Alberto0235/USB3.2-Hub-4Port/Images/Stackup.png

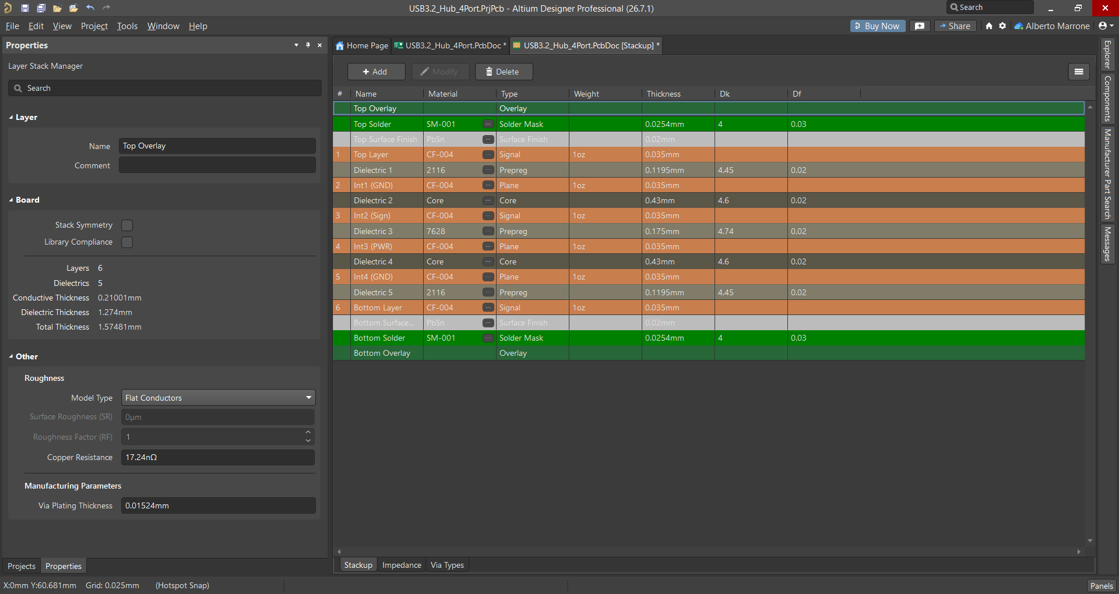
Images/Stackup.png
