Alberto0235/USB3.2-Hub-4Port/Images/Bringup_PowerMeter_Setup.png

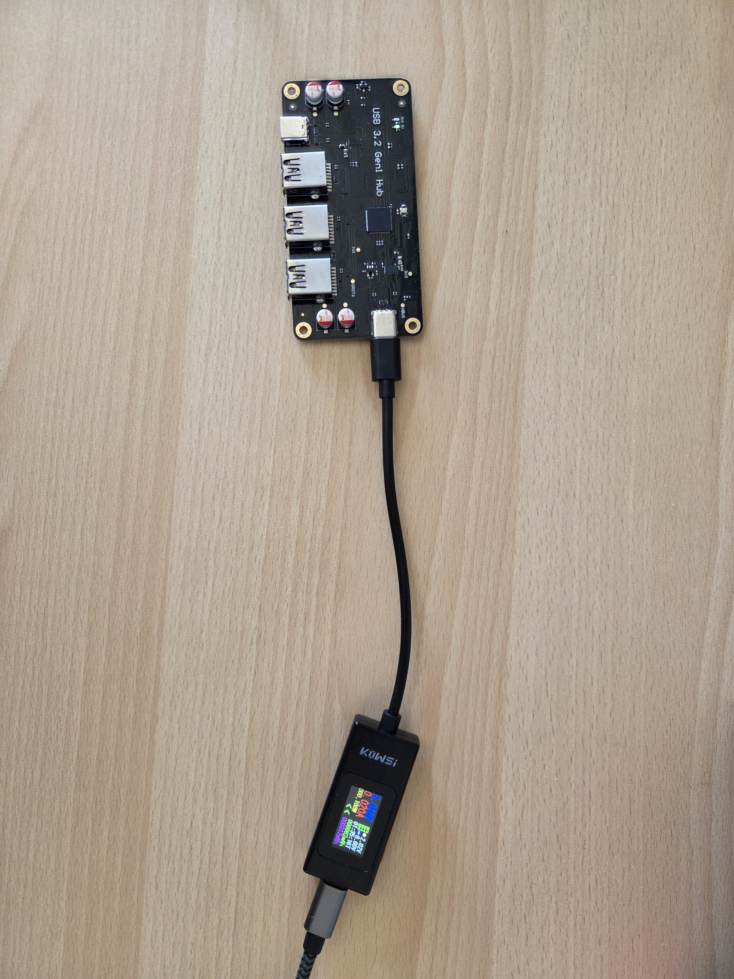
Images/Bringup_PowerMeter_Setup.png
