Alberto0235/USB3.2-Hub-4Port/Images/Bringup_TP_1V1.png

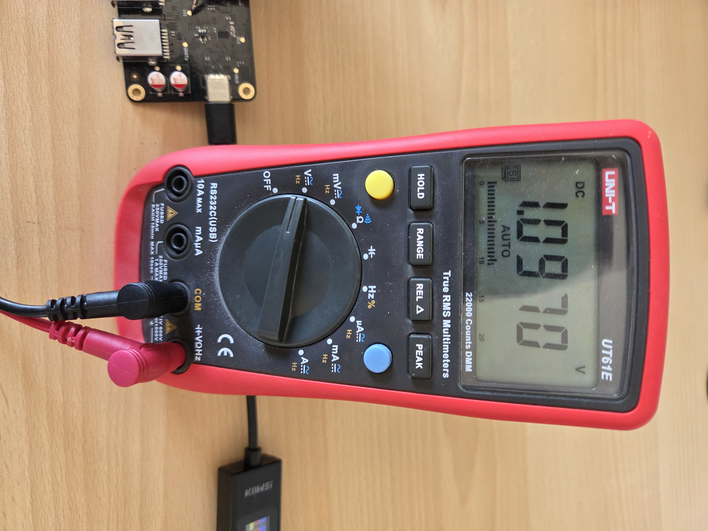
Images/Bringup_TP_1V1.png
